martinr6b/OpnBrewer/images/IMG_20250621_153032667.jpg

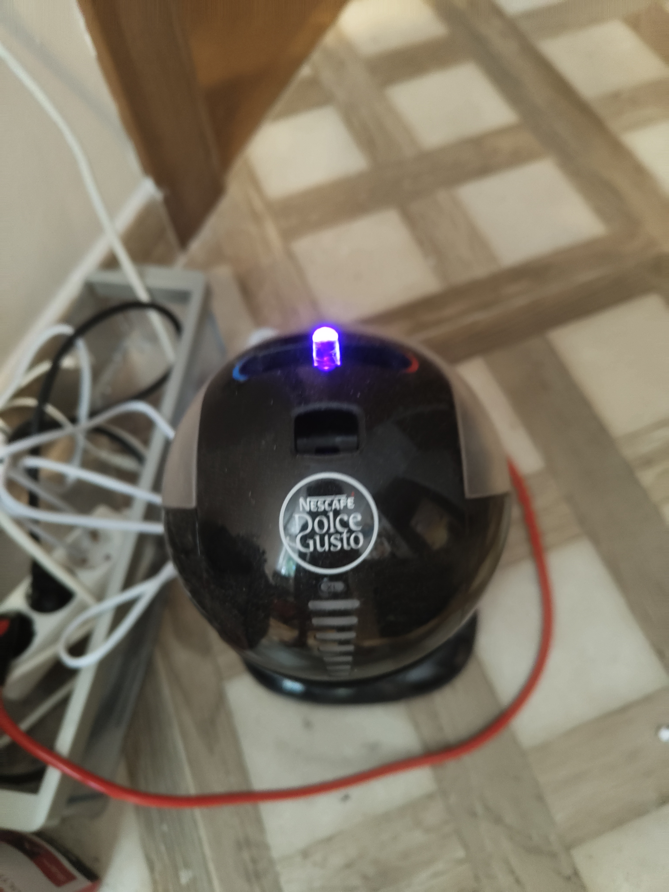
images/IMG_20250621_153032667.jpg
