martinr6b/OpnBrewer/images/IMG_20250621_153042396.jpg

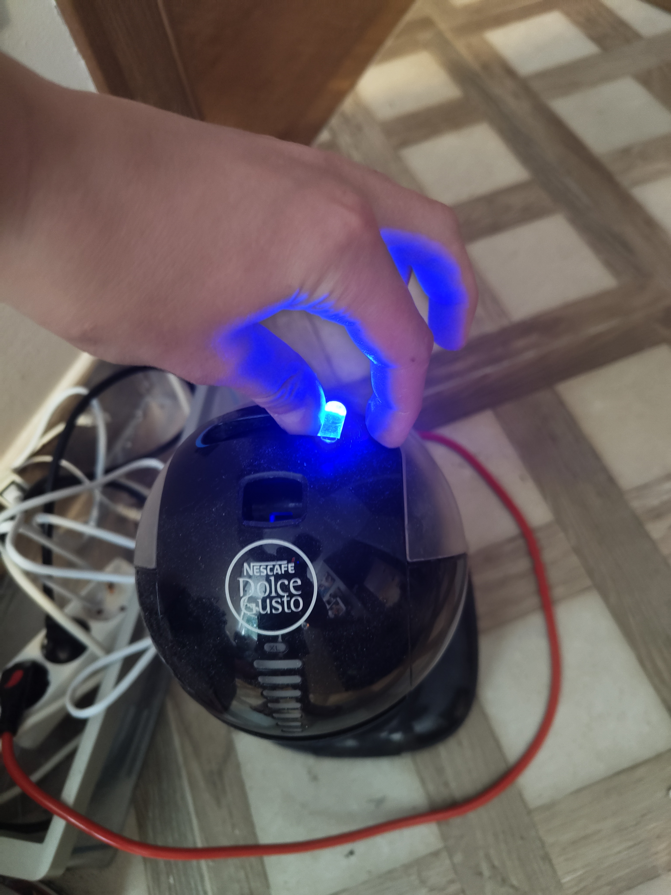
images/IMG_20250621_153042396.jpg
