martinr6b/OpnBrewer/images/IMG_20250621_154229270.jpg

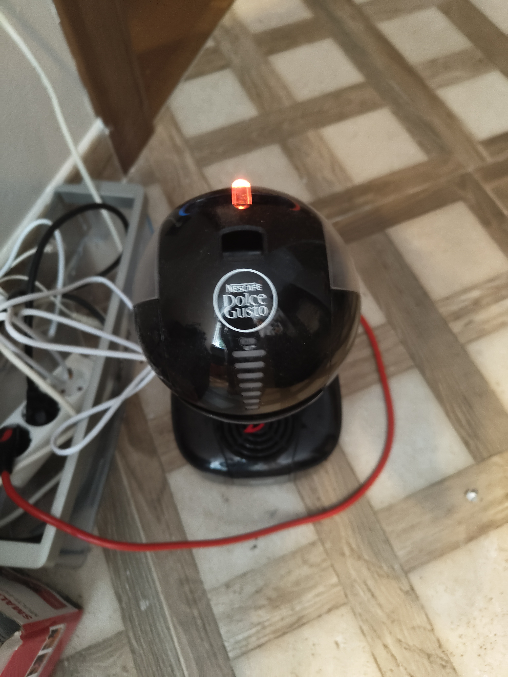
images/IMG_20250621_154229270.jpg
